anyWareSculpture/physical/arduino/Test sketches/HandshakeTester/MPR121.cpp

/*******************************************************************************

 Bare Conductive MPR121 library
 ------------------------------
 
 MPR121.cpp - MPR121 class implementation file
 
 Based on code by Jim Lindblom and plenty of inspiration from the Freescale 
 Semiconductor datasheets and application notes.
 
 Bare Conductive code written by Stefan Dzisiewski-Smith and Peter Krige.
 
 This work is licensed under a Creative Commons Attribution-ShareAlike 3.0 
 Unported License (CC BY-SA 3.0) http://creativecommons.org/licenses/by-sa/3.0/
 
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
*******************************************************************************/

extern "C" {
	#include <stdlib.h>
	#include <string.h>
	#include <inttypes.h>
}

#include "MPR121.h"
#include <Arduino.h>

#define NOT_INITED_BIT 0
#define ADDRESS_UNKNOWN_BIT 1
#define READBACK_FAIL_BIT 2
#define OVERCURRENT_FLAG_BIT 3
#define OUT_OF_RANGE_BIT 4

MPR121_t::MPR121_t(){
	Wire.begin();	
	address = 0x5C;    // default address is 0x5C, for use with Bare Touch Board
	ECR_backup = 0x00;
	running = false;
	error = 1<<NOT_INITED_BIT; // initially, we're not initialised
	touchData = 0;
	lastTouchData = 0;	
}

void MPR121_t::setRegister(unsigned char reg, unsigned char value){

	bool wasRunning = false;;

	if(reg==ECR){	// if we are modding ECR, update our internal running status
		if(value&0x3F){
			running = true;
		} else {
			running = false;
		} 
	} else if(reg<CTL0){
		wasRunning = running;
		if(wasRunning) stop(); 	// we should ALWAYS be in stop mode for this
								// unless modding ECR or GPIO / LED register
	}
	
    Wire.beginTransmission(address);
    Wire.write(reg);
    Wire.write(value);
    if(Wire.endTransmission()!=0){ 
    	error |= 1<<ADDRESS_UNKNOWN_BIT; // set address unknown bit
    } else {
    	error &= ~(1<<ADDRESS_UNKNOWN_BIT); 
    }
    
    if(wasRunning) run();		// restore run mode if necessary
}

unsigned char MPR121_t::getRegister(unsigned char reg){
	unsigned char scratch;

    Wire.beginTransmission(address); 
    Wire.write(reg); // set address to read from our requested register
    Wire.endTransmission(false); // repeated start
    Wire.requestFrom(address,(unsigned char)1);  // just a single byte
    if(Wire.endTransmission()!=0){
    	error |= 1<<ADDRESS_UNKNOWN_BIT;
    } else {
    	error &= ~(1<<ADDRESS_UNKNOWN_BIT);
    }
    scratch = Wire.read();
    // auto update errors for registers with error data
    if(reg == TS2 && ((scratch&0x80)!=0)){
    	error |= 1<<OVERCURRENT_FLAG_BIT;	
    } else {
    	error &= ~(1<<OVERCURRENT_FLAG_BIT);	
    }
    if((reg == OORS1 || reg == OORS2) && (scratch!=0)){
    	error |= 1<<OUT_OF_RANGE_BIT;    
    } else {
    	error &= ~(1<<OUT_OF_RANGE_BIT);    
    }
    return scratch;
}

bool MPR121_t::begin(){
	error &= ~(1<<NOT_INITED_BIT); // clear NOT_INITED error flag

	if(reset()){
		// default values...
		applySettings(&defaultSettings);
		return true;
	} else {
		return false;
	}
	
}

bool MPR121_t::begin(unsigned char address){
	if(address>=0x5A && address<=0x5D) // addresses only valid 0x5A to 0x5D 
	{
		this->address = address; // need to be specific here
	}
	return begin();
}

void MPR121_t::goSlow(){
	TWBR = ((F_CPU / 100000L) - 16) / 2; // set I2C clock to 100kHz
}

void MPR121_t::goFast(){
	TWBR = ((F_CPU / 400000L) - 16) / 2; // set I2C clock to 400kHz
}

void MPR121_t::run(){
	if(!isInited()) return;
	setRegister(ECR, ECR_backup); // restore backup to return to run mode
}

void MPR121_t::stop(){
	if(!isInited()) return;
	ECR_backup = getRegister(ECR);	// backup ECR to restore when we enter run
	setRegister(ECR, ECR_backup & 0xC0); // turn off all electrodes to stop
}

bool MPR121_t::reset(){
	// return true if we successfully reset a device at the 
	// address we are expecting
	
	// AFE2 is one of the few registers that defaults to a non-zero value - 
	// checking it is sensible as reading back an incorrect value implies 
	// something went wrong - we also check TS2 bit 7 to see if we have an 
	// overcurrent flag set
	
	setRegister(SRST, 0x63); // soft reset

	if(getRegister(AFE2)!=0x24){
		error |= 1<<READBACK_FAIL_BIT;
	} else {
		error &= ~(1<<READBACK_FAIL_BIT);
	}

	if((getRegister(TS2)&0x80)!=0){
		error |= 1<<OVERCURRENT_FLAG_BIT;
	} else {
		error &= ~(1<<OVERCURRENT_FLAG_BIT);
	}	

	if(getError()==NOT_INITED || getError()==NO_ERROR){ // if our only error is that we are not inited...
		return true;
	} else {
		return false;
	}
}

void MPR121_t::applySettings(MPR121_settings_t *settings){
	bool wasRunning = running;
	if(wasRunning) stop();  // can't change most regs when running - checking 
							// here avoids multiple stop() / run() calls

	setRegister(MHDR,settings->MHDR);
	setRegister(NHDR,settings->NHDR);
	setRegister(NCLR,settings->NCLR);
	setRegister(FDLR,settings->FDLR);
	setRegister(MHDF,settings->MHDF);
	setRegister(NHDF,settings->NHDF);
	setRegister(NCLF,settings->NCLF);
	setRegister(FDLF,settings->FDLF);
	setRegister(NHDT,settings->NHDT);
	setRegister(NCLT,settings->NCLT);
	setRegister(FDLT,settings->FDLT);
	setRegister(MHDPROXR,settings->MHDPROXR);
	setRegister(NHDPROXR,settings->NHDPROXR);
	setRegister(NCLPROXR,settings->NCLPROXR);
	setRegister(FDLPROXR,settings->FDLPROXR);
	setRegister(MHDPROXF,settings->MHDPROXF);
	setRegister(NHDPROXF,settings->NHDPROXF);
	setRegister(NCLPROXF,settings->NCLPROXF);
	setRegister(FDLPROXF,settings->FDLPROXF);
	setRegister(NHDPROXT,settings->NHDPROXT);
	setRegister(NCLPROXT,settings->NCLPROXT);
	setRegister(FDLPROXT,settings->FDLPROXT);
  	setRegister(DTR, settings->DTR);
	setRegister(AFE1, settings->AFE1);  
	setRegister(AFE2, settings->AFE2);
	setRegister(ACCR0, settings->ACCR0);
	setRegister(ACCR1, settings->ACCR1);
	setRegister(USL, settings->USL); 
	setRegister(LSL, settings->LSL); 
	setRegister(TL, settings->TL); 
	
	setRegister(ECR, settings->ECR);	
	
	error &= ~(1<<NOT_INITED_BIT); // clear not inited error as we have just inited!
	setTouchThreshold(settings->TTHRESH);
	setReleaseThreshold(settings->RTHRESH);
	setInterruptPin(settings->INTERRUPT);	
	
	if(wasRunning) run();	
}

mpr121_error_t MPR121_t::getError(){

	// important - this resets the IRQ pin - as does any I2C comms

	getRegister(OORS1);	// OOR registers - we may not have read them yet,
	getRegister(OORS2);	// whereas the other errors should have been caught

	// order of error precedence is determined in this logic block

	if(!isInited()) return NOT_INITED; // this has its own checker function

	if((error & (1<<ADDRESS_UNKNOWN_BIT)) != 0){
		return ADDRESS_UNKNOWN;	
	} else if((error & (1<<READBACK_FAIL_BIT)) != 0){
		return READBACK_FAIL;
	} else if((error & (1<<OVERCURRENT_FLAG_BIT)) != 0){
		return OVERCURRENT_FLAG;
	} else if((error & (1<<OUT_OF_RANGE_BIT)) != 0){
		return OUT_OF_RANGE;
	} else return NO_ERROR;
	
}

void MPR121_t::clearError(){
	error = 0;
}

bool MPR121_t::isRunning(){
	return running;
}

bool MPR121_t::isInited(){
	return (error & (1<<NOT_INITED_BIT)) == 0;
}

void MPR121_t::updateTouchData(){
	if(!isInited()) return;
	
	lastTouchData = touchData;
	touchData = (unsigned int)getRegister(TS1) + ((unsigned int)getRegister(TS2)<<8);
}

bool MPR121_t::getTouchData(unsigned char electrode){
	if(electrode>12 || !isInited()) return false; // avoid out of bounds behaviour

	return((touchData>>electrode)&1);
}

unsigned char MPR121_t::getNumTouches(){
	if(!isInited()) return(0xFF);
	
	unsigned char scratch = 0;
	for(unsigned char i=0; i<13; i++){
		if(getTouchData(i)) scratch++;
	}
	
	return(scratch);
}

bool MPR121_t::getLastTouchData(unsigned char electrode){
	if(electrode>12 || !isInited()) return false; // avoid out of bounds behaviour

	return((lastTouchData>>electrode)&1);
}

bool MPR121_t::updateFilteredData(){
	if(!isInited()) return(false);
	unsigned char LSB, MSB;

    Wire.beginTransmission(address); 
    Wire.write(E0FDL); 	// set address register to read from the start of the 
    					//filtered data
    Wire.endTransmission(false); // repeated start
  
    if(Wire.requestFrom(address,(unsigned char)26)==26){
		for(int i=0; i<13; i++){ // 13 filtered values
		  LSB = Wire.read();
		  MSB = Wire.read();
		  filteredData[i] = ((MSB << 8) | LSB);
		} 
		return(true);    
    } else {
    	// if we don't get back all 26 values we requested, don't update the FDAT values
    	// and return false
		return(false);     
    }
}

int MPR121_t::getFilteredData(unsigned char electrode){
	if(electrode>12 || !isInited()) return(0xFFFF); // avoid out of bounds behaviour

	return(filteredData[electrode]);
}

bool MPR121_t::updateBaselineData(){
	if(!isInited()) return(false);

    Wire.beginTransmission(address); 
    Wire.write(E0BV); 	// set address register to read from the start of the 
    					// baseline data
    Wire.endTransmission(false); // repeated start
  
    if(Wire.requestFrom(address,(unsigned char)13)==13){
		for(int i=0; i<13; i++){ // 13 filtered values
		  baselineData[i] = Wire.read()<<2;
		}    
		return(true); 
    } else {
		for(int i=0; i<13; i++){         
    	// if we don't get back all 26 values we requested, don't update the FDAT values
    	// and return false
		return(false); 
		}        
    }
}

int MPR121_t::getBaselineData(unsigned char electrode){
	if(electrode>12 || !isInited()) return(0xFFFF); // avoid out of bounds behaviour
  
	return(baselineData[electrode]);
}

bool MPR121_t::isNewTouch(unsigned char electrode){
	if(electrode>12 || !isInited()) return(false); // avoid out of bounds behaviour	
	return((getLastTouchData(electrode) == false) && (getTouchData(electrode) == true));
}

bool MPR121_t::isNewRelease(unsigned char electrode){
	if(electrode>12 || !isInited()) return(false); // avoid out of bounds behaviour	
	return((getLastTouchData(electrode) == true) && (getTouchData(electrode) == false));
}

void MPR121_t::updateAll(){
	updateTouchData();
	updateBaselineData();
	updateFilteredData();
}

void MPR121_t::setTouchThreshold(unsigned char val){
	if(!isInited()) return;
	bool wasRunning = running;
	
	if(wasRunning) stop();	// can only change thresholds when not running
							// checking here avoids multiple stop() / run() 
							// calls
	
	for(unsigned char i=0; i<13; i++){
		setTouchThreshold(i, val);
	}
	
	if(wasRunning) run();
}

void MPR121_t::setTouchThreshold(unsigned char electrode, unsigned char val){
	if(electrode>12 || !isInited()) return; // avoid out of bounds behaviour
	
	// this relies on the internal register map of the MPR121
	setRegister(E0TTH + (electrode<<1), val); 																							
}

void MPR121_t::setReleaseThreshold(unsigned char val){
	if(!isInited()) return;
	bool wasRunning = running;
	
	if(wasRunning) stop();	// can only change thresholds when not running
							// checking here avoids multiple stop / starts
	
	for(unsigned char i=0; i<13; i++){
		setReleaseThreshold(i,val);
	}
	
	if(wasRunning) run();
}

void MPR121_t::setReleaseThreshold(unsigned char electrode, unsigned char val){
	if(electrode>12 || !isInited()) return; // avoid out of bounds behaviour

	// this relies on the internal register map of the MPR121
	setRegister(E0RTH + (electrode<<1), val); 	
}

unsigned char MPR121_t::getTouchThreshold(unsigned char electrode){
	if(electrode>12 || !isInited()) return(0xFF); // avoid out of bounds behaviour
	return(getRegister(E0TTH+(electrode<<1)));
}
unsigned char MPR121_t::getReleaseThreshold(unsigned char electrode){
	if(electrode>12 || !isInited()) return(0xFF); // avoid out of bounds behaviour
	return(getRegister(E0RTH+(electrode<<1)));
}

void MPR121_t::setInterruptPin(unsigned char pin){
	// :: here forces the compiler to use Arduino's pinMode, not MPR121's
	if(!isInited()) return;
	::pinMode(pin, INPUT_PULLUP);
	interruptPin = pin;		
	
}

bool MPR121_t::touchStatusChanged(){
	// :: here forces the compiler to use Arduino's digitalRead, not MPR121's
	return(!::digitalRead(interruptPin));
}

void MPR121_t::setProxMode(mpr121_proxmode_t mode){

	if(!isInited()) return;

	bool wasRunning = running;

	if(wasRunning) stop();

	switch(mode){
		case DISABLED:
			ECR_backup &= ~(3<<4);	// ELEPROX[0:1] = 00
			break;
		case PROX0_1:
			ECR_backup |=  (1<<4);	// ELEPROX[0:1] = 01
			ECR_backup &= ~(1<<5);			
			break;
		case PROX0_3:
			ECR_backup &= ~(1<<4);	// ELEPROX[0:1] = 10
			ECR_backup |=  (1<<5);			
			break;
		case PROX0_11:
			ECR_backup |=  (3<<4);	// ELEPROX[0:1] = 11
			break;
	}
	
	if(wasRunning) run();
}

void MPR121_t::setNumDigPins(unsigned char numPins){
	if(!isInited()) return;
	bool wasRunning = running;

	if(numPins>8) numPins = 8; // maximum number of GPIO pins is 8 out of 12
	
	if(wasRunning){
		stop(); // have to stop to change ECR
	}
	ECR_backup = (0x0F&(12-numPins)) | (ECR_backup&0xF0);
	if(wasRunning){
		run();
	}
	
}

void MPR121_t::pinMode(unsigned char electrode, mpr121_pinf_t mode){

	// only valid for ELE4..ELE11
	if(electrode<4 || electrode >11 || !isInited()) return; 
											 			
	// LED0..LED7											 
	unsigned char bitmask = 1<<(electrode-4);											 
											 
	switch(mode){
		case INPUT_PU:
			// EN = 1
			// DIR = 0
			// CTL0 = 1
			// CTL1 = 1
			setRegister(EN, getRegister(EN) | bitmask);
			setRegister(DIR, getRegister(DIR) & ~bitmask);
			setRegister(CTL0, getRegister(CTL0) | bitmask);
			setRegister(CTL1, getRegister(CTL1) | bitmask);		
			break;
		case INPUT_PD:
			// EN = 1
			// DIR = 0
			// CTL0 = 1
			// CTL1 = 0
			setRegister(EN, getRegister(EN) | bitmask);
			setRegister(DIR, getRegister(DIR) & ~bitmask);
			setRegister(CTL0, getRegister(CTL0) | bitmask);
			setRegister(CTL1, getRegister(CTL1) & ~bitmask);		
			break;		
		case OUTPUT_HS:
			// EN = 1
			// DIR = 1
			// CTL0 = 1
			// CTL1 = 1
			setRegister(EN, getRegister(EN) | bitmask);
			setRegister(DIR, getRegister(DIR) | bitmask);
			setRegister(CTL0, getRegister(CTL0) | bitmask);
			setRegister(CTL1, getRegister(CTL1) | bitmask);						
			break;		
		case OUTPUT_LS:
			// EN = 1
			// DIR = 1
			// CTL0 = 1
			// CTL1 = 0
			setRegister(EN, getRegister(EN) | bitmask);
			setRegister(DIR, getRegister(DIR) | bitmask);
			setRegister(CTL0, getRegister(CTL0) | bitmask);
			setRegister(CTL1, getRegister(CTL1) & ~bitmask);							
			break;			
	}
}

void MPR121_t::pinMode(unsigned char electrode, int mode){
	if(!isInited()) return;
	
	// this is to catch the fact that Arduino prefers its definition of INPUT 
	// and OUTPUT to ours...
	
	unsigned char bitmask = 1<<(electrode-4);	
	
	if(mode == OUTPUT){ 
		// EN = 1
		// DIR = 1
		// CTL0 = 0
		// CTL1 = 0
		setRegister(EN, getRegister(EN) | bitmask);
		setRegister(DIR, getRegister(DIR) | bitmask);
		setRegister(CTL0, getRegister(CTL0) & ~bitmask);
		setRegister(CTL1, getRegister(CTL1) & ~bitmask);				
			
	} else if(mode == INPUT){
		// EN = 1
		// DIR = 0
		// CTL0 = 0
		// CTL1 = 0
		setRegister(EN, getRegister(EN) | bitmask);
		setRegister(DIR, getRegister(DIR) & ~bitmask);
		setRegister(CTL0, getRegister(CTL0) & ~bitmask);
		setRegister(CTL1, getRegister(CTL1) & ~bitmask);						
	} else {
		return; // anything that isn't a 1 or 0 is invalid
	}
}

void MPR121_t::digitalWrite(unsigned char electrode, unsigned char val){
	
	// avoid out of bounds behaviour
	
	if(electrode<4 || electrode>11 || !isInited()) return; 
	
	if(val){
		setRegister(SET, 1<<(electrode-4));
	} else {
		setRegister(CLR, 1<<(electrode-4));
	}
}

void MPR121_t::digitalToggle(unsigned char electrode){
	
	// avoid out of bounds behaviour
	
	if(electrode<4 || electrode>11 || !isInited()) return; 
	
	setRegister(TOG, 1<<(electrode-4));	
}

bool MPR121_t::digitalRead(unsigned char electrode){
	
	// avoid out of bounds behaviour
	
	if(electrode<4 || electrode>11 || !isInited()) return false; 
	
	return(((getRegister(DAT)>>(electrode-4))&1)==1);
}

void MPR121_t::analogWrite(unsigned char electrode, unsigned char value){
	// LED output 5 (ELE9) and output 6 (ELE10) have a PWM bug
	// https://community.freescale.com/thread/305474

	// avoid out of bounds behaviour

	if(electrode<4 || electrode>11 || !isInited()) return; 
	
	unsigned char shiftedVal = value>>4;	
	
	if(shiftedVal > 0){
		setRegister(SET, 1<<(electrode-4)); // normal PWM operation 
	} else {
		// this make a 0 PWM setting turn off the output	
		setRegister(CLR, 1<<(electrode-4)); 
	}
	
	unsigned char scratch;
  
	switch(electrode-4){

	case 0:
	  scratch = getRegister(PWM0);
	  setRegister(PWM0, (shiftedVal & 0x0F) | (scratch & 0xF0));
	  break;
	case 1:
	  scratch = getRegister(PWM0);
	  setRegister(PWM0, ((shiftedVal & 0x0F)<<4) | (scratch & 0x0F));
	  break;
	case 2:
	  scratch = getRegister(PWM1);
	  setRegister(PWM1, (shiftedVal & 0x0F) | (scratch & 0xF0));
	  break;
	case 3:
	  scratch = getRegister(PWM1);
	  setRegister(PWM1, ((shiftedVal & 0x0F)<<4) | (scratch & 0x0F));
	  break;
	case 4:
	  scratch = getRegister(PWM2);
	  setRegister(PWM2, (shiftedVal & 0x0F) | (scratch & 0xF0));
	  break;
	case 5:
	  scratch = getRegister(PWM2);
	  setRegister(PWM2, ((shiftedVal & 0x0F)<<4) | (scratch & 0x0F));
	  break;
	case 6:
	  scratch = getRegister(PWM3);
	  setRegister(PWM3, (shiftedVal & 0x0F) | (scratch & 0xF0));
	  break;
	case 7:
	  scratch = getRegister(PWM3);
	  setRegister(PWM3, ((shiftedVal & 0x0F)<<4) | (scratch & 0x0F));
	  break;
	}

	
}

MPR121_t MPR121 = MPR121_t();
